Clewsy/grinder_timer/data/O1_oled_dimensions.jpg

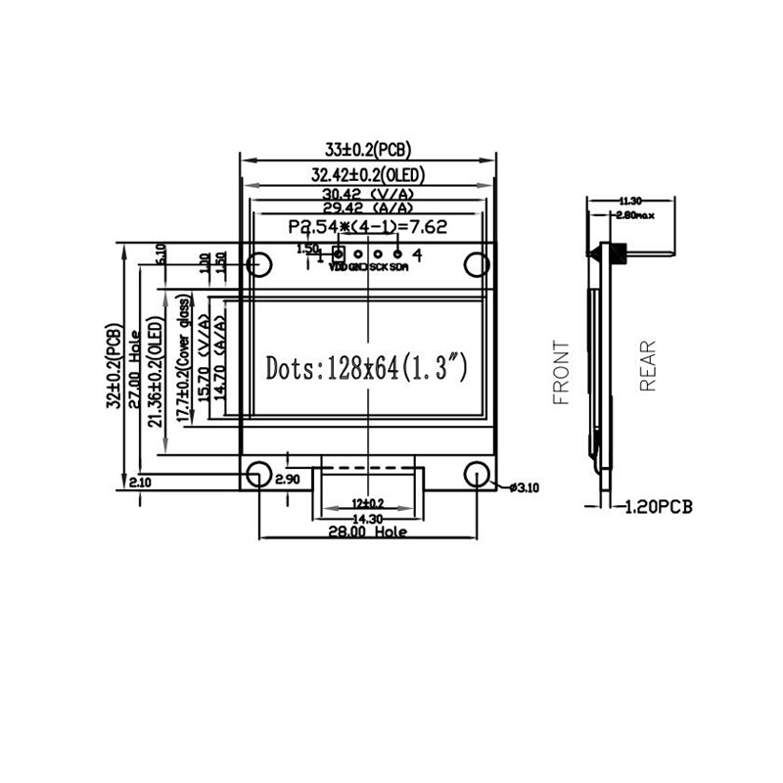
data/O1_oled_dimensions.jpg
