Clewsy/grinder_timer/firmware/src/grinder_timer.cpp

#include "grinder_timer.hpp"

// An overflow of the configured timer counter register triggers this interrupt sub-routine.
// It increments a counter until a set value is reached at which point it enables "sleep mode".
ISR(SLEEPER_INT_VECTOR)
{
	sleep_timer.counter++;
	if(sleep_timer.counter > SLEEP_COUNTER) sleep_mode(true);
}

// A pin-change on any keypad button triggers this sub-routine.
ISR(BUTTON_PCI_VECTOR)
{
	_delay_ms(BUTTON_DEBOUNCE_MS);	// Wait for the button de-bounce duration.

	if	(grinder.get_status() && buttons.any())	grind(false);		// If grinding, cancel grind with any button.
	else if	(sleep_timer.sleeping && buttons.any())	sleep_mode(false);	// If sleeping, wake device but skip button action.
	else if	(!grinder.get_status())
	{
		sleep_timer.reset();							// Reset sleep mode timer counter.
		if	(buttons.check(BUTTON_UP))	handle_up_down(UP);		// Increase current preset timer.
		else if	(buttons.check(BUTTON_DOWN))	handle_up_down(DOWN);		// Decrease current preset timer.
		else if (buttons.check(BUTTON_LEFT))	handle_left_right(LEFT);	// Select preset to the left.
		else if (buttons.check(BUTTON_RIGHT))	handle_left_right(RIGHT);	// Select preset to the right.
		else if (buttons.check(BUTTON_GRIND))	grind(true);			// Start grinding.
	}
}

// An overflow of the timer output compare register triggers this interrupt sub-routine.
// Configured to vary the LED brightness at desired interval to create a pulsing effect.
ISR(PULSER_INT_VECTOR)
{
	led.interrupt_handler();
}

// An overflow of the timer counter register triggers this interrupt sub-routine.
// Configured to use external 32.768kHz crystal and therefore provide accurate timing in sixteenths of a second.
ISR(CLOCK_INT_VECTOR)
{
	if(rtc.counter > 0)	rtc.counter--;	// Count down to zero.
	else			grind(false);	// If reached zero, stop grinding.
	refresh_timer();			// Update the display with the remaining countdown duration.
}

// Call this function to enter or cancel "sleep mode" which is effectively disabling the oled and enabling the LED pulse effect.
void sleep_mode(bool go_to_sleep)
{
	oled.enable_screen(!go_to_sleep);		// Turn the screen on or off.
	sleep_timer.enable(!go_to_sleep);		// If we want to sleep then we can disable the sleep_timer.  Otherwise enable it to resume counting.
	led.mode(LED_PULSE >> (1 - go_to_sleep));	// Will set the led to pulsing in sleep mode, otherwise just on.
	sleep_timer.reset();				// This function always resets the sleep_timer regardless of sleeping flag.
	if(sleep_timer.sleeping) while(buttons.any()) {}// If sleeping, wait until the button is released so the actual button action is ignored.
	sleep_timer.sleeping = go_to_sleep;		// Set the "sleeping" flag.
}

// Called to alter the  value of the currently selected preset.
// Can be adjusted up or down in increments of 0.25 seconds.
// Oled is also refreshed accordingly.
void change_preset_value(int8_t up_or_down)
{
	preset.timer[preset.selected] += (up_or_down * 4);							// Either +=4 or -=4.
	if(preset.timer[preset.selected] > PRESET_MAX_VALUE) preset.timer[preset.selected] = PRESET_MAX_VALUE;	// Upper limit.
	if(preset.timer[preset.selected] < PRESET_MIN_VALUE) preset.timer[preset.selected] = PRESET_MIN_VALUE;	// Lower limit.

	rtc.counter = preset.timer[preset.selected];	// Update the timer value.
	refresh_timer();				// Update the timer display.
}

// Handle user pressing and releasing, or pressding and holding either the up or down button.
// Up and down buttons are used to adjust the value of the currently selected preset.
void handle_up_down(int8_t up_or_down)
{
	change_preset_value(up_or_down);	// Update the preset value and refresh the display.

	uint16_t hold_timer = BUTTON_LONG_PRESS;
	while((buttons.any()) && ((hold_timer--) > 0)) _delay_ms(1);	// Wait until button is released or long-press duration elapses.

	while(buttons.any())	// Until the button is released.
	{
		change_preset_value(up_or_down);
		_delay_ms(BUTTON_FAST_CHANGE);		
	}
}

// Function called to update display when scrolling left or right.
void handle_left_right(int8_t left_or_right)
{
	preset.selected += (left_or_right);	// Equivalent to either ++ or --.

	if(preset.selected == (PRESET_D + 1))	preset.selected = PRESET_A;	// D->A
	if(preset.selected == 0xFF)		preset.selected = PRESET_D;	// D<-A

	rtc.counter = preset.timer[preset.selected];	// Update the timer value.
	refresh_display();				// Update the timer and preset menu displays.

	preset.update_eeprom();	// Update the presets in eeprom if the previously selected changed.

	while(buttons.any()) {}	// Wait until the button is released.
}

// Initiate or cease grinding.
void grind(bool grind)
{
	grinder.on(grind);	// Turn on or off the grinder motor.
	rtc.enable(grind);	// Enable or disable the countdown timer.
	if(!grind)		// If stopped grinding, pause at zero for a moment before resetting the rtc.
	{
		_delay_ms(RELAY_RESET_DELAY);
		rtc.counter = preset.timer[preset.selected];
		refresh_timer();
	}
	preset.update_eeprom();	// Update the presets in eeprom (will only update if value differed from eeprom when the grind was started).
	sleep_mode(false);	// Restart the sleep mode timer.
	led.mode(!grind);	// LED off while grinding, on when finished.
}

// Update the preset selection menu section of the OLED.
void refresh_menu(void)
{
	unsigned char preset_icons[5] = {'A','B','C','D',0};	// Default icons i.e. not selected.
	preset_icons[preset.selected] += 4;			// Charaters E, F, G & H actually show as inverted A, B, C & D to identify selected preset.
	oled.print_string(preset_icons, Preset_Icons, 0, 34);	// Print the preset icons string to the OLED.

	oled.print_char(LEFT_ARROW, Arrows, 0, 19);		// Print a left-pointing arrow to the left of the preset icons.
	oled.print_char(RIGHT_ARROW, Arrows, 0, 94);		// Print a right-pointing arrow to the right of the preset icons.
}

// Update the clock/timer section of the OLED.
void refresh_timer(void)
{
	unsigned char digits_string[6] = {'0','0','.','0','0',0};		// Want to display the current timer value as ##.## seconds.
	digits_string[0] = (((rtc.counter >> 4) / 10) + '0');			// Convert counter value 10s to ascii.
	digits_string[1] = (((rtc.counter >> 4) % 10) + '0');			// Convert counter value 1s to ascii.
	digits_string[3] = (((uint16_t)(rtc.counter * 0.625) % 10) + '0');	// Convert counter value 10ths to ascii.
	digits_string[4] = (((uint16_t)(rtc.counter * 6.25) % 10) + '0');	// Convert counter value 100ths to ascii.

	oled.print_string(digits_string, DSEG7_Classic_Bold_32, 3, 5);		// Write the array to the display.
}

// Refresh bot main sections of the display - the timer section and the preset menu section.
void refresh_display(void)
{
	refresh_menu();
	refresh_timer();
}

// Display a silly "animation" when powered on.
void splash(void)
{
	oled.map_bits(LOGO_CLEWS, sizeof(LOGO_CLEWS));					// Show bitmap for a duration.
	_delay_ms(300);
	oled.map_bits(LOGO_HAD, sizeof(LOGO_HAD));					// Show bitmap for a duration.
	_delay_ms(300);
	oled.clear_screen();
	oled.draw_box(0, 0, 64, 128);							// Box around the outermost border of the oled.
	oled.print_string((unsigned char*)"grind(coffee);", Roboto_Mono_12, 3, 15);	// Text centered (roughly).
	for(uint8_t i = 1; i < 16; i*=2) oled.scroll(SCROLL_DN, (8 / i), i);		// Scrolling animation, iterates 4 times:
											// 1st: 8 cycles, 1ms delay.
											// 2nd: 4 cycles, 2ms delay.
											// 3rd: 2 cycles, 4ms delay.
											// 4th: 1 cycle,  8ms delay.
	_delay_ms(2000);
	oled.clear_screen();
}

// Initialise the various hardware peripherals.
void hardware_init()
{
	grinder.init();					// Initialise the grinder motor relay (relay class).
	buttons.init();					// Initialise the buttons (keypad class).
	led.init(LED_ON);				// Initialise the led (pulser class) and set the initial mode (on, off or pulsing).
	preset.init();					// Initialise the saved (to eeprom) values for the four presets and the currently selected preset.
	rtc.init(preset.timer[preset.selected]);	// Initialise the real-time clock (clock class) and set the initial counter value.
	oled.init();					// Initialise the OLED display (sh1106 class).
	sleep_timer.init();				// Initialise the sleeper timer.
	sei();						// Globally enable all interrupts.
}

int main(void)
{
	hardware_init();
	splash();
	refresh_display();
	sleep_timer.enable(true);
	buttons.enable();

	while(1)
	{
		//Driven by interrupts.
	}

	return(7);
}
