Clewsy/grinder_timer/firmware/include/sh1106_bitmaps.h

//A bitmap consists of 8192 pixels broken into 1024 8-bit segments.
// If the bitmap contains fewer than 1024 segments, the map_bits() function draws the present segments then assumes the remaining segments are blank.

const uint8_t BLANK[] PROGMEM = {0x00};		// This "array" can be sent to the map_bits() function to effectvely clear the screen.

const uint8_t LOGO_HAD[] PROGMEM = {
//	  01					      010						020						  030						    040						      050						060		     				  070						    080						      090						100						  110						    120					    128
	0x00,0x00,0x00,0x00,0x00,0x00,0x00,0x00,0x00,0x00,0x00,0x00,0x00,0x00,0x00,0x00,0x00,0x00,0x00,0x00,0x00,0x00,0x00,0x00,0x00,0x00,0x00,0x00,0x00,0x80,0x80,0x00,0x00,0x00,0x00,0x00,0x03,0x03,0x07,0x8f,0x9f,0xff,0xfe,0xfc,0xfc,0xfc,0xf0,0x00,0x00,0x00,0x00,0x00,0x00,0x00,0x00,0x00,0x00,0x00,0x00,0x00,0x00,0x00,0x00,0x00,0x00,0x00,0x00,0x00,0x00,0x00,0x00,0x00,0x00,0x00,0x00,0x00,0x00,0x00,0x00,0x00,0x00,0xe0,0xf8,0xfc,0xfc,0xfe,0xff,0xff,0x9f,0x8f,0x03,0x03,0x01,0x00,0x00,0x00,0x00,0x80,0x80,0x80,0x00,0x00,0x00,0x00,0x00,0x00,0x00,0x00,0x00,0x00,0x00,0x00,0x00,0x00,0x00,0x00,0x00,0x00,0x00,0x00,0x00,0x00,0x00,0x00,0x00,0x00,0x00,0x00,
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
};
