Clewsy/grinder_timer/firmware/src/i2c.cpp

#include "i2c.hpp"

// Initialise the I2C hardware.
void i2c::init(void)
{
//	I2C_TWBR = 32;	// TWBR = 32 Gives SCL Frequency = 100kHz if F_CPU is 8MHz, 12.5kHz if F_CPU is 1MHz.
	I2C_TWBR = 2;	// TWBR = 2 Gives SCL Frequency = 400kHz if F_CPU is 8MHz, 50kHz if F_CPU is 1MHz.
			// TWBR: TWI Bit-Rate Register - Used to set the TWI (I2C) Frequency (SCL).
			// SCL frequency = (CPU Freq)/( 16 + 2*(TWBR)*(PrescalerValue)).
			// Note, PrescalerValue default = 1, otherwise set in TWSR with bits TWPS[1:0].
			// TWSR: TWI Status Register.

	I2C_TWCR |= (1 << TWEN);	// TWCR: TWI Control Register
					// TWEN: TWI Enable Bit - turns on TWI (I2C) hardware.
}

// Set the I2C start condition.
void i2c::start(void)
{
	I2C_TWCR = ((1 << TWEN) | (1 << TWSTA) | (1 << TWINT));	// A TWI start is initiated by setting the following bits on TWCR:
								// TWEN - TWI enable.
								// TWSTA - TWI Start Condition.
								// TWINT - Clear TWINT flag (will be set at completion of operation).
	wait_for_complete();					// Wait until previous operation is complete.

}

// Set the I2C stop condition.
void i2c::stop(void)
{
	I2C_TWCR = ((1 << TWEN) | (1 << TWSTO) | (1 << TWINT));	// A TWI stop is initiated by setting the following bits on TWCR:
								// TWEN - TWI enable.
								// TWSTO - TWI Stop Condition.
								// TWINT - Clear TWINT flag (will be set at completion of operation).
}

// Transmit a byte.
void i2c::write_byte(uint8_t address)
{
	I2C_TWDR = address;				// TWDR: TWI (I2C) Data Register.
	I2C_TWCR = ((1 << TWEN) | (1 << TWINT));	// Have to clear the int flag (and keep enabled).
	wait_for_complete();				// Wait until the int flag is again set.
}

// Receive a byte (then send acknowledgement).
uint8_t i2c::read_byte_ack(void)
{
	I2C_TWCR |= ((1 << TWINT) | (1 << TWEN) | (1 << TWEA));	// Have to clear the int flag, keep enabled and set the acknowledge bit.
	wait_for_complete();					// Wait until the int flag is again set.
	return(I2C_TWDR);					// TWDR: TWI (I2C) Data Register.
}

// Receive a byte (without sending acknowledgement).
uint8_t i2c::read_byte_nack(void)
{
	I2C_TWCR |= ((1 << TWINT) | (1 << TWEN));	// Have to clear the int flag and keep enabled.
	wait_for_complete();				// Wait until the int flag is again set.
	return(I2C_TWDR);				// TWDR: TWI (I2C) Data Register.
}

// Wait until the TWI (I2C) interrupt flag is set indicating an operation has just completed.
void i2c::wait_for_complete(void)
{
	while(!(TWCR0 & (1 << TWINT))) {}	// Loop until current TWI (I2C) operation is complete (bit is set).
						// TWINT: TWI Interrupt Flag - Set flag indicates current job has finished.
						// Note, TWINT must be cleared by software - this indicates start of next operation.
						// Extra note, reading TWINT gives status of flag (1=set, 0=clear) but to clear the flag,
						// software must write 1 to TWINT.
}
